Hanz-Tech/midi-adapter-v2-hardware/photos/layout.JPG

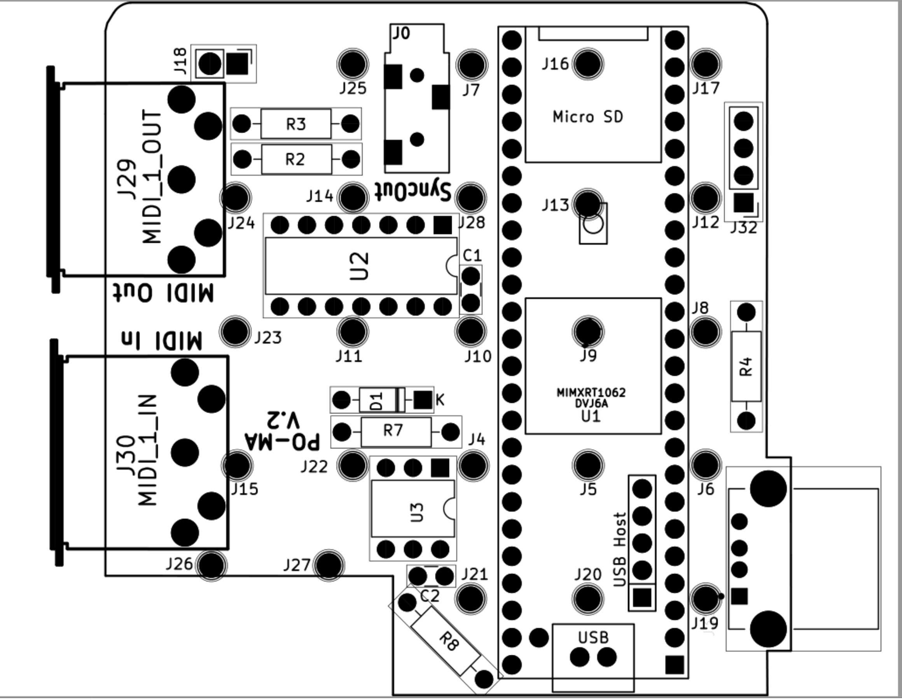
photos/layout.JPG
