Hanz-Tech/midi-adapter-v2-hardware/photos/pomav2-1.jpg

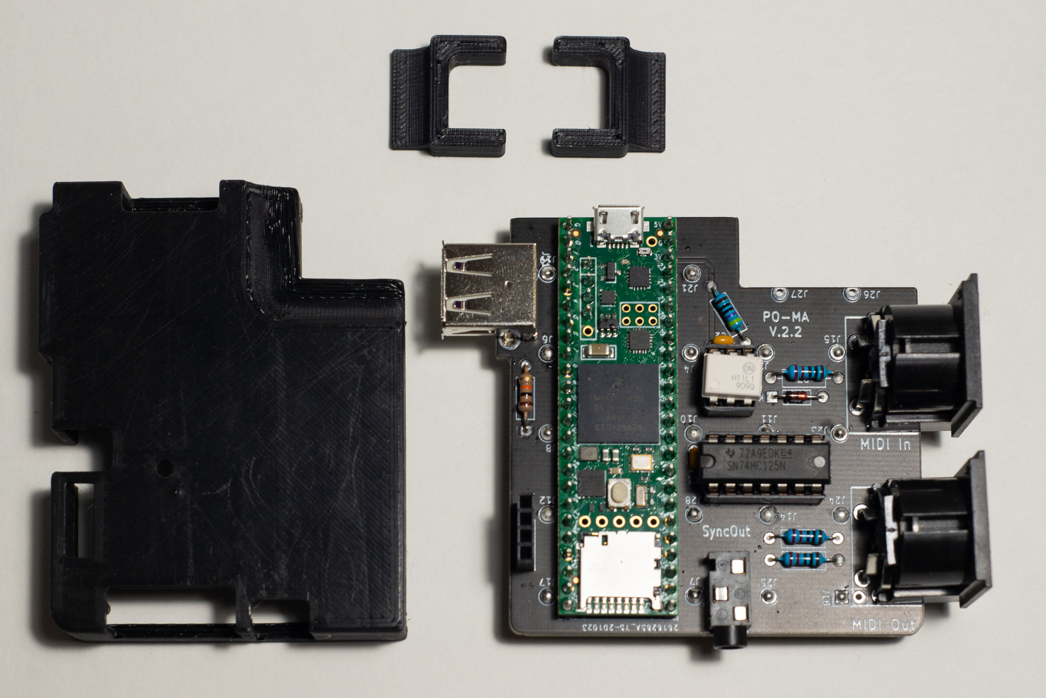
photos/pomav2-1.jpg
