Hanz-Tech/midi-adapter-v2-hardware/photos/pomav2-18.jpg

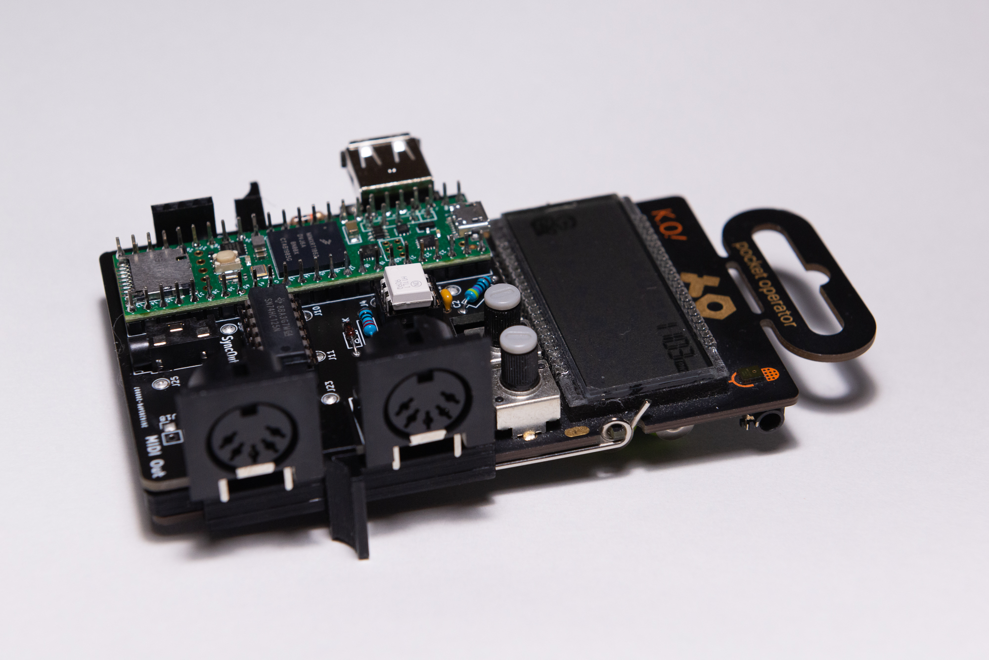
photos/pomav2-18.jpg
