Hanz-Tech/midi-adapter-v2-hardware/photos/pomav2-19.jpg

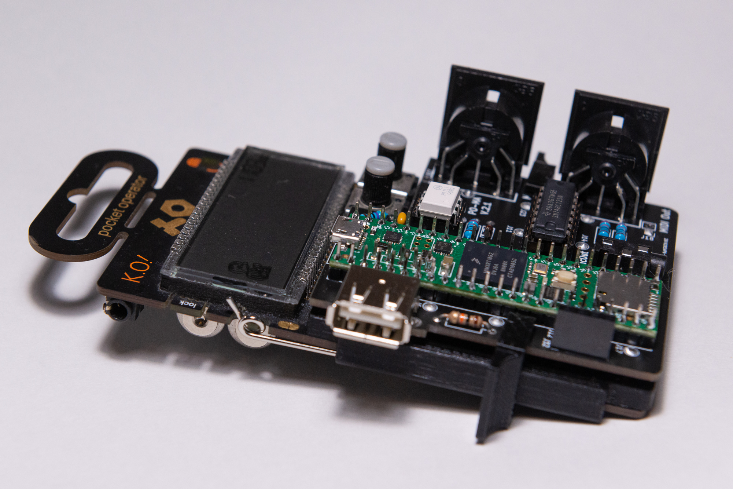
photos/pomav2-19.jpg
