Hanz-Tech/midi-adapter-v2-hardware/photos/assembly/01.jpg

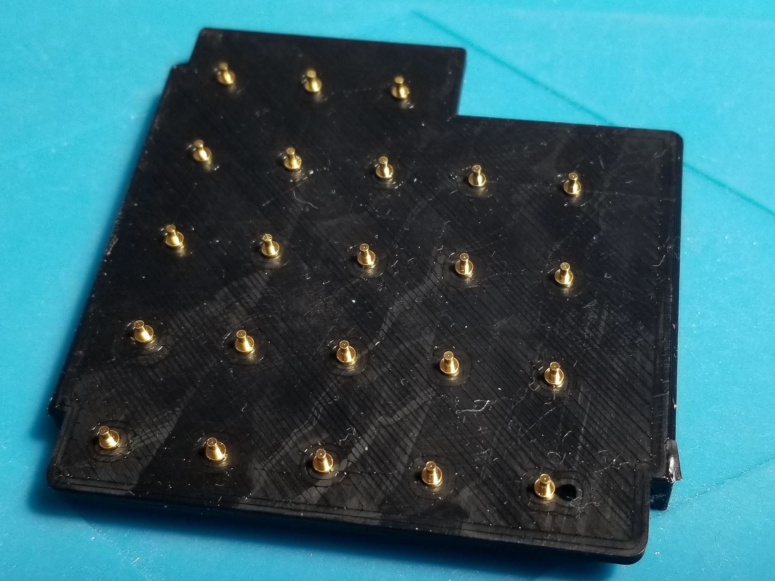
photos/assembly/01.jpg
