Hanz-Tech/midi-adapter-v2-hardware/photos/assembly/03.jpg

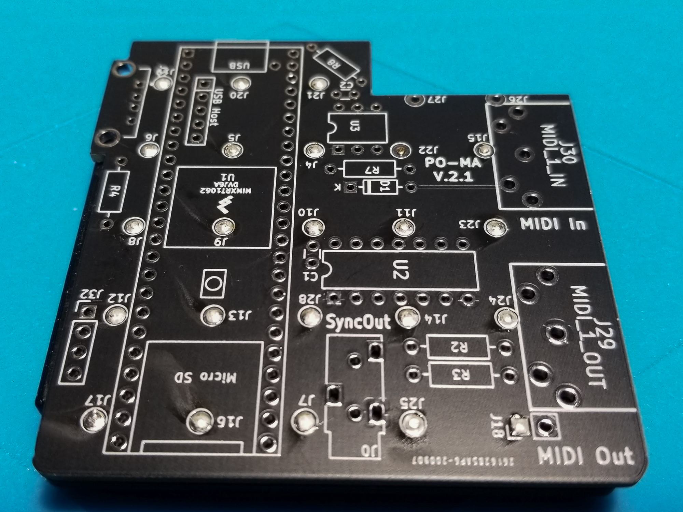
photos/assembly/03.jpg
