Hanz-Tech/midi-adapter-v2-hardware/photos/assembly/04.jpg

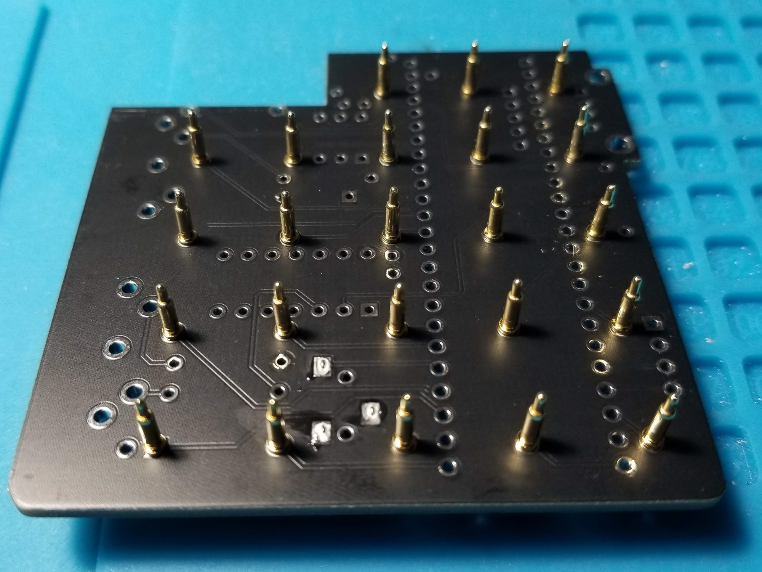
photos/assembly/04.jpg
