Hanz-Tech/midi-adapter-v2-hardware/photos/assembly/05.jpg

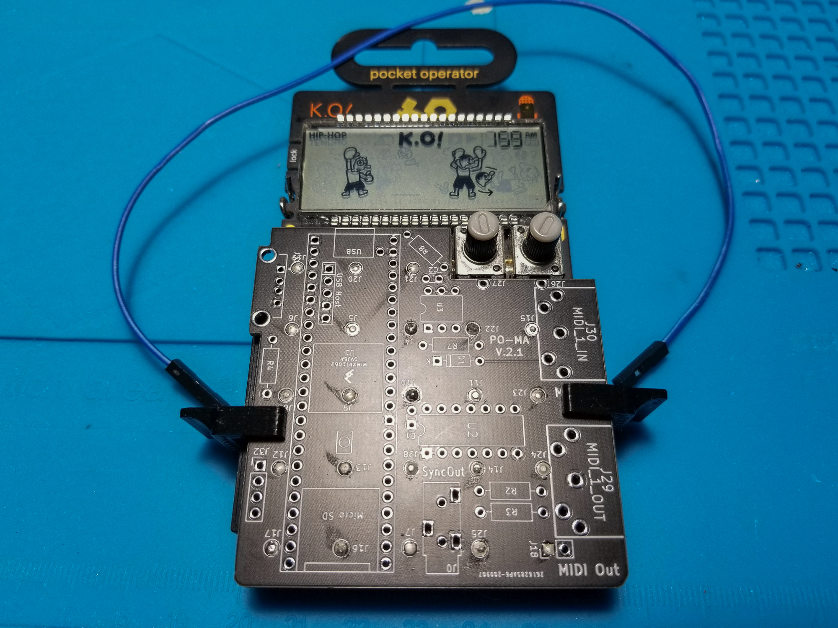
photos/assembly/05.jpg
