Hanz-Tech/midi-adapter-v2-hardware/photos/assembly/08.jpg

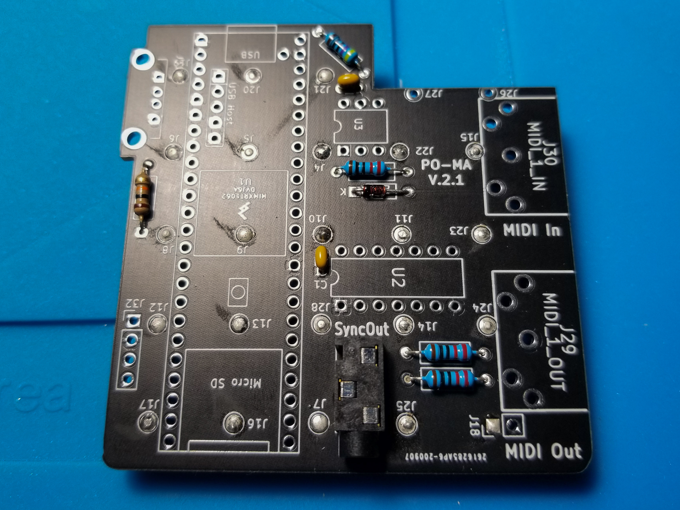
photos/assembly/08.jpg
