Hanz-Tech/midi-adapter-v2-hardware/photos/assembly/010_5.jpg

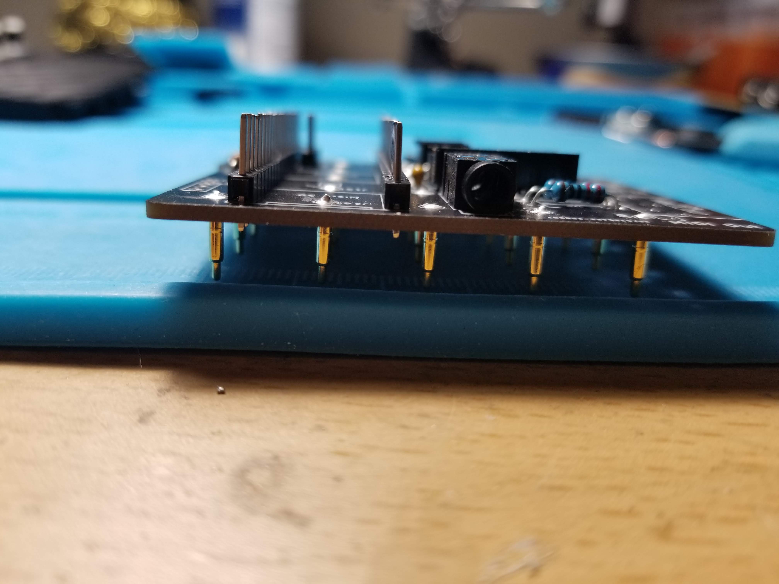
photos/assembly/010_5.jpg
