Hanz-Tech/midi-adapter-v2-hardware/photos/assembly/011.jpg

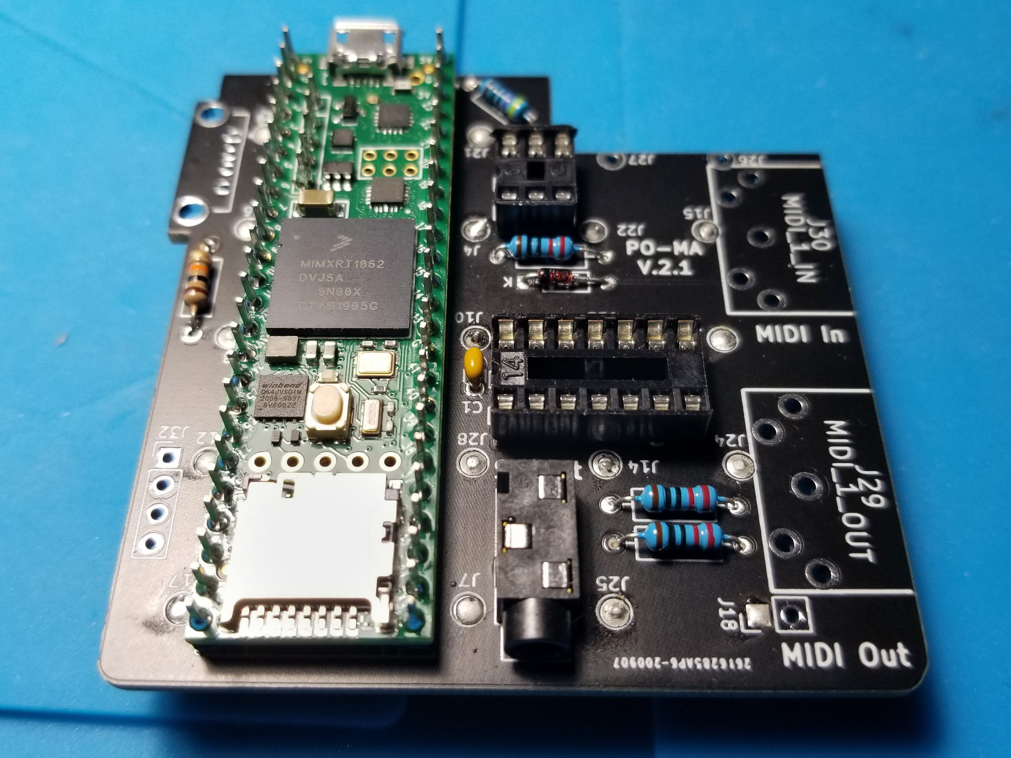
photos/assembly/011.jpg
