Hanz-Tech/midi-adapter-v2-hardware/photos/assembly/012.jpg

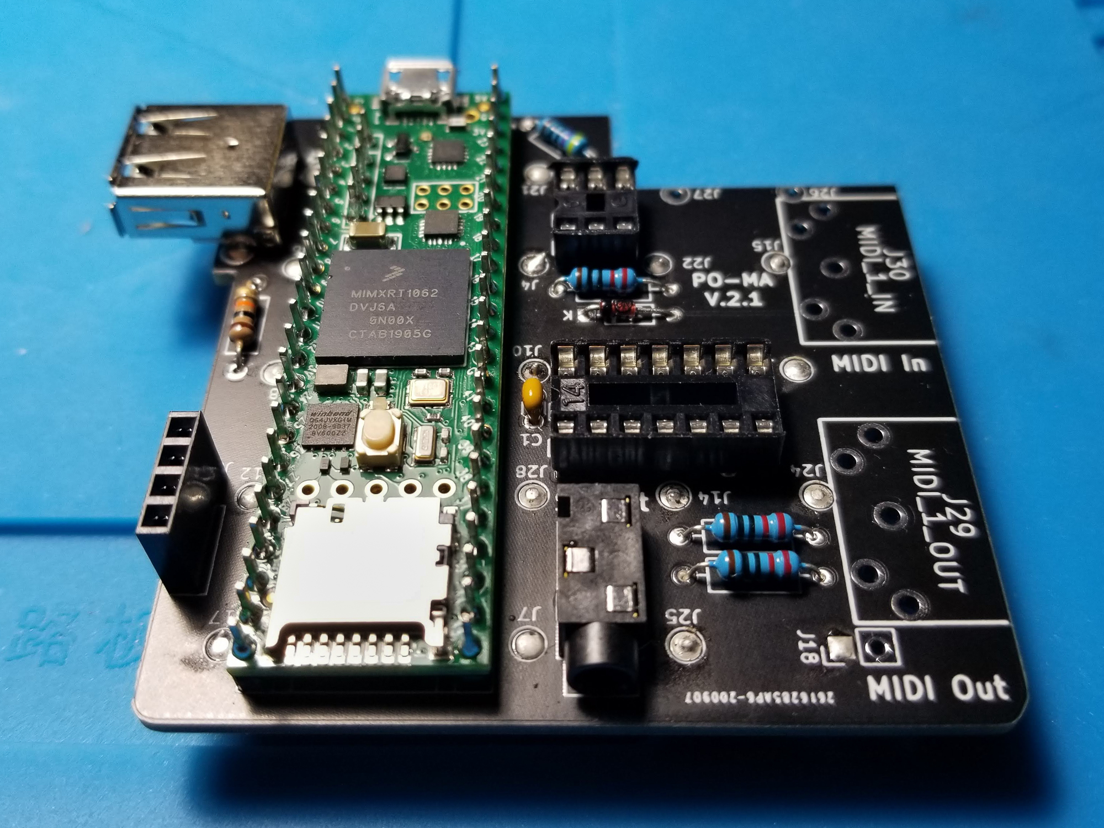
photos/assembly/012.jpg
