Hanz-Tech/midi-adapter-v2-hardware/photos/assembly/014.jpg

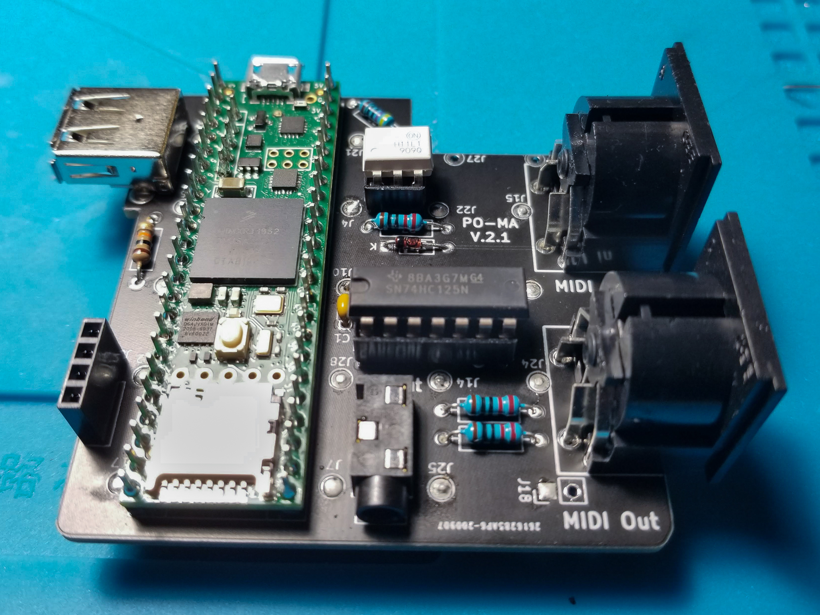
photos/assembly/014.jpg
